newdigate/teensy-eurorack/software/examples/graphics/01_heart/README.md

# draw an antialiased heart curve using beziers



heart
* requires [teensy-libcurve](https://github.com/newdigate/teensy-libcurve)
