newdigate/teensy-eurorack/software/examples/ad5754/01_write_ad5754/README.md

* a simple example demonstrating how to write to a single ad5754 d/a using SPI 
