newdigate/teensy-eurorack/software/examples/ad5754/02_write_both_ad5754/README.md

A simple example showing how to write to both ad5754 d/a converters using SPI
