newdigate/teensy-eurorack/software/examples/audio/libscope/README.md

# Examples using teensy-libscope

* these projects require [teensy-audio-libtftscope](https://github.com/newdigate/teensy-audio-libtftscope)
