newdigate/teensy-eurorack/software/examples/audio/midside_encode/README.md

# videos
* side-channel stereo audio separation with teensy 4.0:
side-channel stereo audio separation with teensy 4.0 (https://www.youtube.com/watch?v=N0IBevm4hTQ)
