newdigate/teensy-eurorack/software/examples/audio/display_levels/01_display_levels/README.md

* display incoming audio levels 

# dependencies
* [PaulStoffregen](https://github.com/PaulStoffregen)
  * [cores](https://github.com/PaulStoffregen/cores)
  * [SPI](https://github.com/PaulStoffregen/SPI)
  * [ST7735_t3](https://github.com/PaulStoffregen/ST7735_t3)
* [newdigate](https://github.com/newdigate)
  *  [teensy-audio-display-components](https://github.com/newdigate/teensy-audio-display-components)
