newdigate/teensy-eurorack/software/examples/audio/codec/02_Play_and_display/README.md

# MP3, AAC audio player



* adapted from [Complete_MP3_AAC_MP4_M4A_example](https://github.com/FrankBoesing/Arduino-Teensy-Codec-lib/tree/master/examples/Complete_MP3_AAC_MP4_M4A_example)

## Dependencies, code adaptions:
* MP3/AAC library code by Frank Boesing.
  * https://github.com/FrankBoesing/Arduino-Teensy-Codec-lib
* JPEGDecoder
  * https://github.com/Bodmer/JPEGDecoder
  * uses picojpeg by Rich Geldreich <richgel99@gmail.com>
    * https://github.com/richgel999/picojpeg
