newdigate/teensy-eurorack/software/examples/audio/codec/01_Mp3FilePlayer/README.md

adapted from [Mp3FilePlayer](https://github.com/FrankBoesing/Arduino-Teensy-Codec-lib/tree/master/examples/Mp3FilePlayer)
