newdigate/teensy-eurorack/software/examples/audio/libscope/04_audio_only_full_bandwidth/README.md

* output sine waves on all audio outputs
* display audio inputs on a scope view
