newdigate/teensy-eurorack/software/examples/audio/libscope/02_input_scopes/README.md

* output sine waves on all audio and cv outputs
* display audio and cv input wave graphs
