newdigate/teensy-eurorack/software/examples/audio/audio_to_cv/01_audio_to_cv/README.md

example demonstrating how to send audio in to cv out
