newdigate/teensy-eurorack/hardware/boards/3d/Yamaichi - PJS008U-3000-0.step

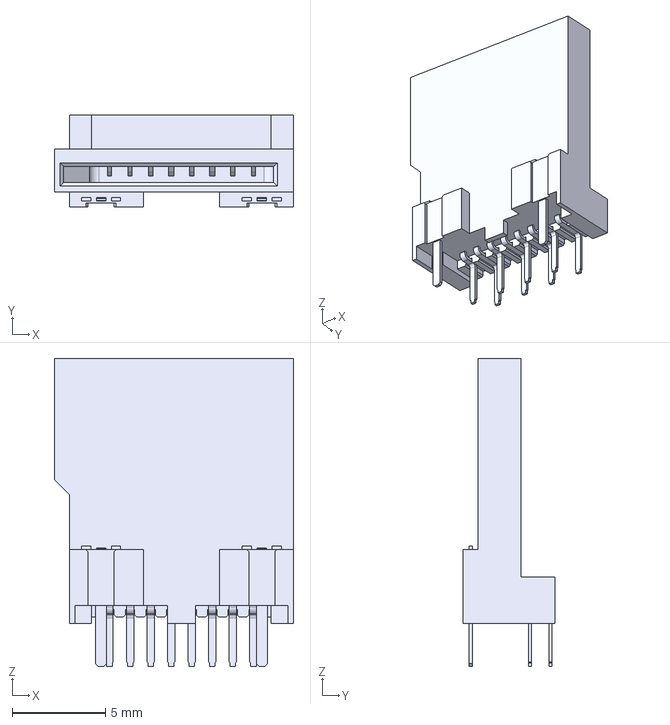
[picture p23: CAD file, 2019-09-27]
hardware/boards/3d/Yamaichi - PJS008U-3000-0.step
12.8 x 4.90 x 16.5 mm
