newdigate/teensy-eurorack/hardware/boards/3d/MIDI DIN 5 v7.step

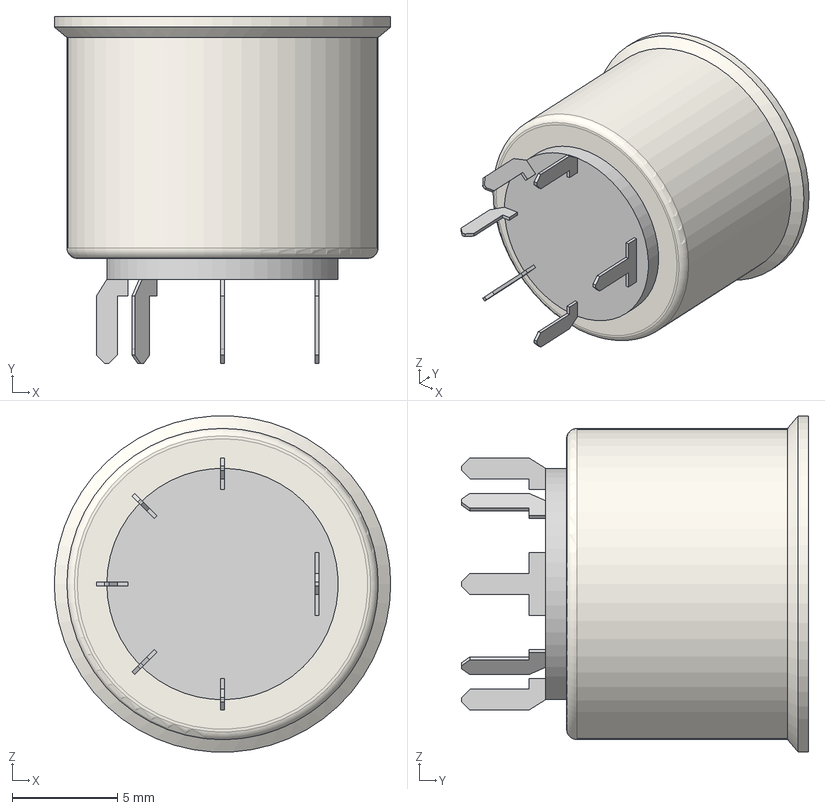
[picture p24: CAD file, 2019-09-27]
hardware/boards/3d/MIDI DIN 5 v7.step
16.0 x 16.5 x 16.0 mm
