newdigate/teensy-eurorack/hardware/boards/3d/ili7735 v6.step

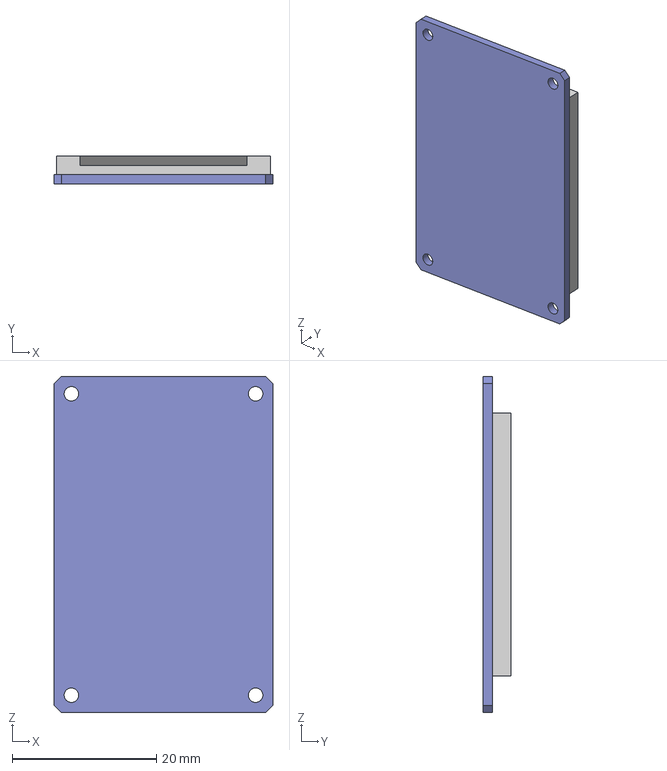
[picture p25: CAD file, 2019-09-27]
hardware/boards/3d/ili7735 v6.step
30.4 x 3.90 x 46.6 mm
