newdigate/teensy-eurorack/hardware/boards/3d/conn_JST_S4B-PH-SM4-TB(LF)(SN).step

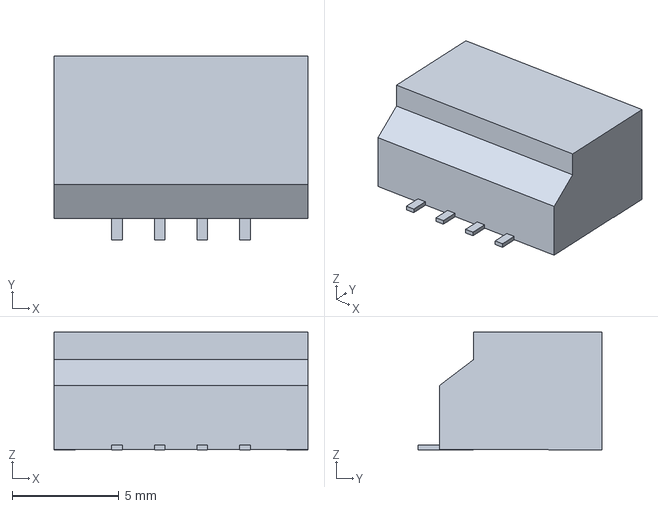
[picture p26: CAD file, 2019-09-27]
hardware/boards/3d/conn_JST_S4B-PH-SM4-TB(LF)(SN).step
11.9 x 8.60 x 5.52 mm
