newdigate/teensy-eurorack/hardware/boards/3d/Conn_Wurth Electronics_61400413321.step

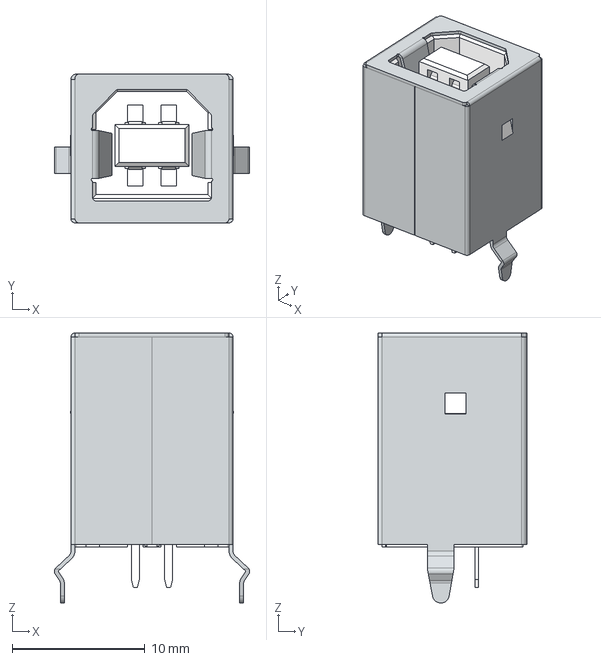
[picture p27: CAD file, 2019-09-27]
hardware/boards/3d/Conn_Wurth Electronics_61400413321.step
14.7 x 11.2 x 20.3 mm
