newdigate/teensy-eurorack/software/examples/tests/knobs/flash-samd/README.md

https://github.com/arduino/ArduinoCore-samd/blob/master/bootloaders/mkrzero/samd21_sam_ba_arduino_mkrzero.bin
