newdigate/teensy-eurorack/software/src/teensy_eurorack_audio.h

//
// Created by Moolet on 09/03/2021.
//

#ifndef TEENSY_EURORACK_TEENSY_EUROACK_AUDIO_H
#define TEENSY_EURORACK_TEENSY_EUROACK_AUDIO_H

// https://github.com/newdigate/teensy-audio-ad5754-ad7606
#include "input_output_spi.h"

#endif //TEENSY_EURORACK_TEENSY_EUROACK_AUDIO_H
